NieBrun/2023-2024-4GP-BESNARD-BRUN/Arduino/Test_HC_05/Test_HC_05.ino

#include <SoftwareSerial.h>
#define rxPin 8 //Broche 11 en tant que RX, � raccorder sur TX du HC-05
#define txPin 7 //Broche 10 en tant que RX, � raccorder sur TX du HC-05
#define baudrate 9600
SoftwareSerial mySerial(rxPin ,txPin); //D�finition du software serial

void setup(){
  pinMode(rxPin,INPUT);
  pinMode(txPin,OUTPUT);
    
  mySerial.begin(baudrate);
  Serial.begin(baudrate);
}

void loop(){
    int i = 0; 
	char someChar[32] ={0};
	//when characters arrive over the serial port...

	while (Serial.available()) {
	   do{
		someChar[i++] = Serial.read();
		delay(3);		
	   }while (Serial.available() > 0);
	   
	   mySerial.println(someChar); 
	   Serial.println(someChar); 
	}
	while (mySerial.available()) {
		Serial.print((char)mySerial.read());
	}
}
